ImShyMike/IRview/images/image-7.png

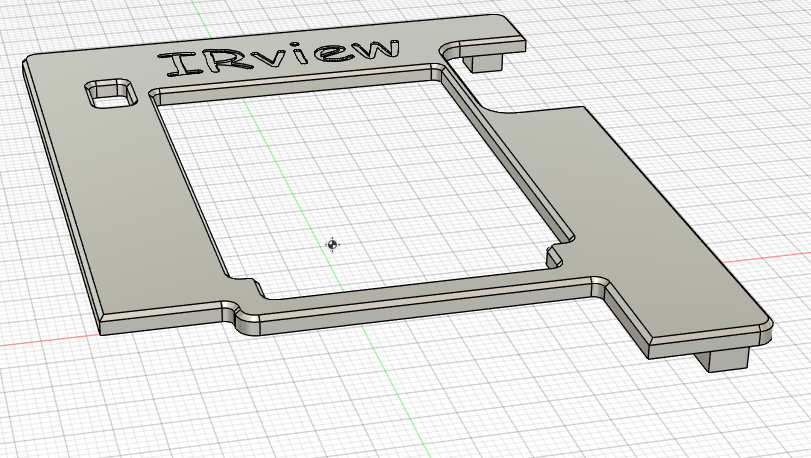
images/image-7.png
