ImShyMike/IRview/images/image-8.png

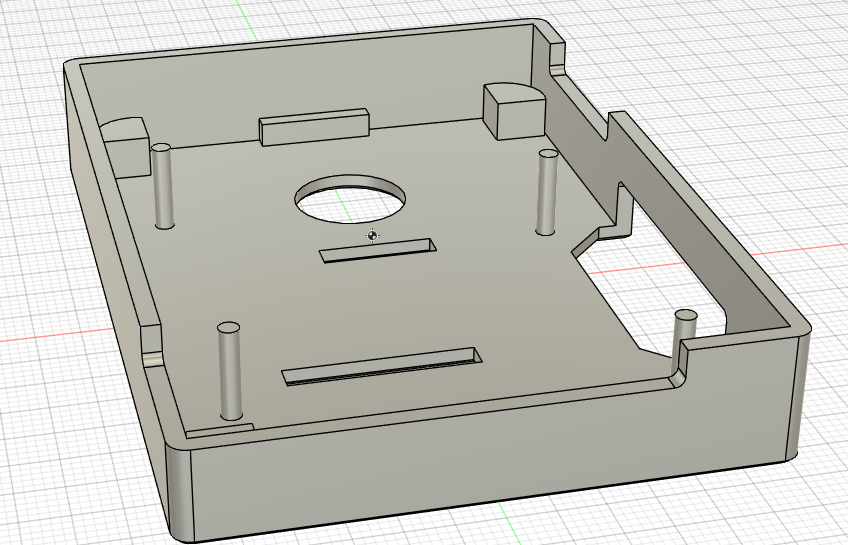
images/image-8.png
